jerinpeter/4wdNavbot/data/mq1.jpg

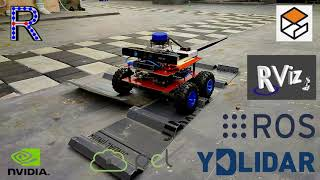
data/mq1.jpg
