jerinpeter/4wdNavbot/data/nano.jpg

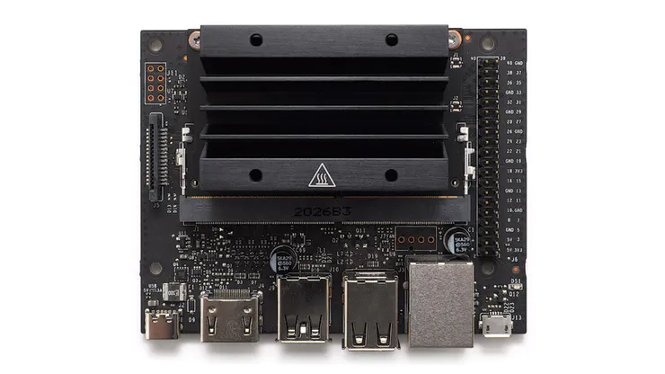
data/nano.jpg
