jerinpeter/4wdNavbot/data/robot7.jpg

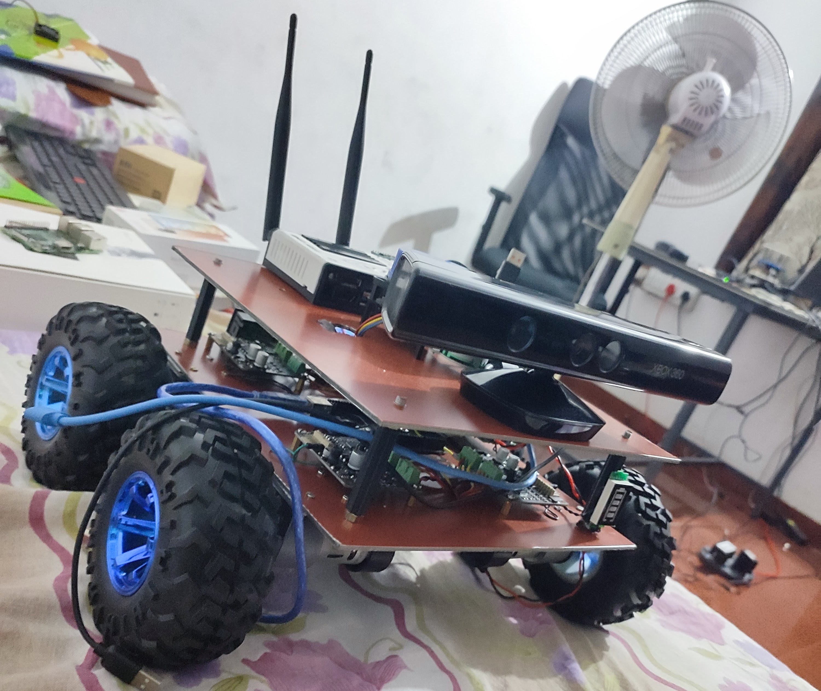
data/robot7.jpg
