jerinpeter/4wdNavbot/data/robot.jpg

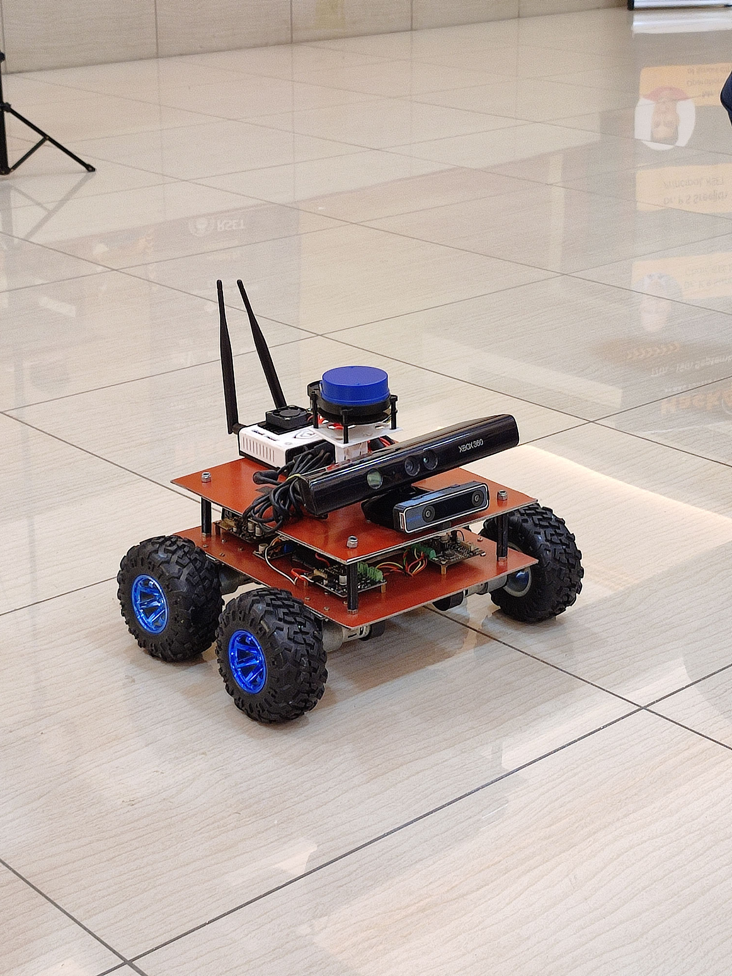
data/robot.jpg
